evankravitz/ECE-3400-Team-1/resources/sensorposition.JPG

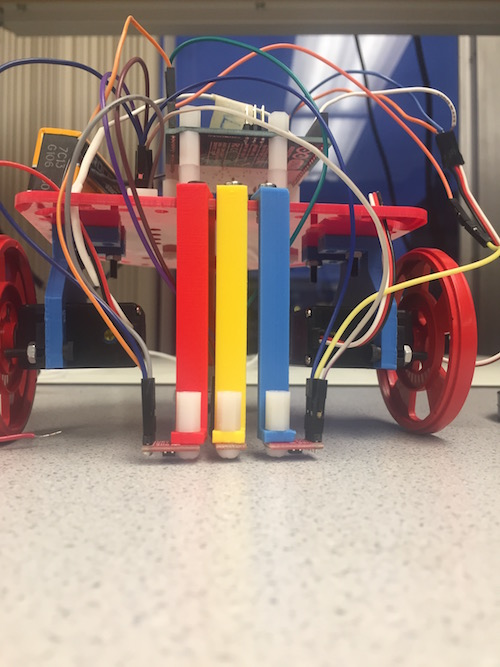
resources/sensorposition.JPG
