evankravitz/ECE-3400-Team-1/resources/lab2irscope.jpg

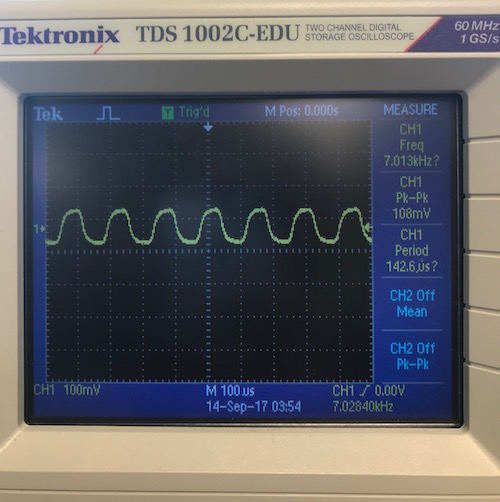
resources/lab2irscope.jpg
