evankravitz/ECE-3400-Team-1/img/portfolio/ethicsbot.gif

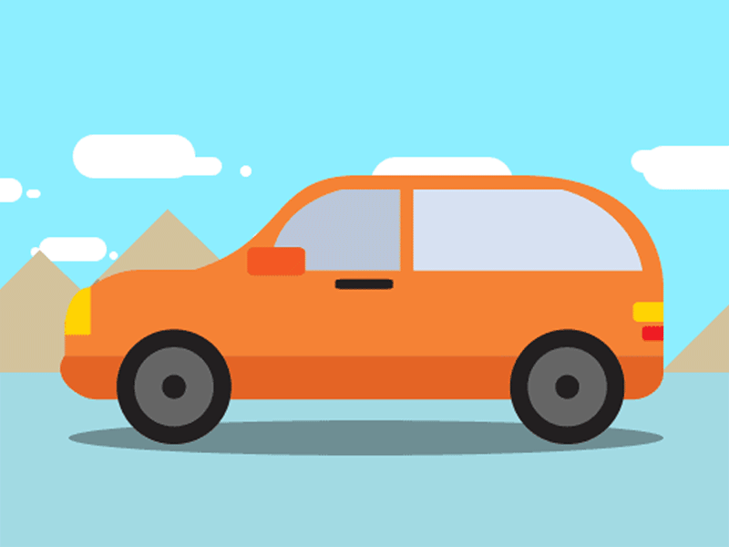
img/portfolio/ethicsbot.gif
