evankravitz/ECE-3400-Team-1/resources/2fc07050c8674d979eb9044ecb1724d5.jpeg

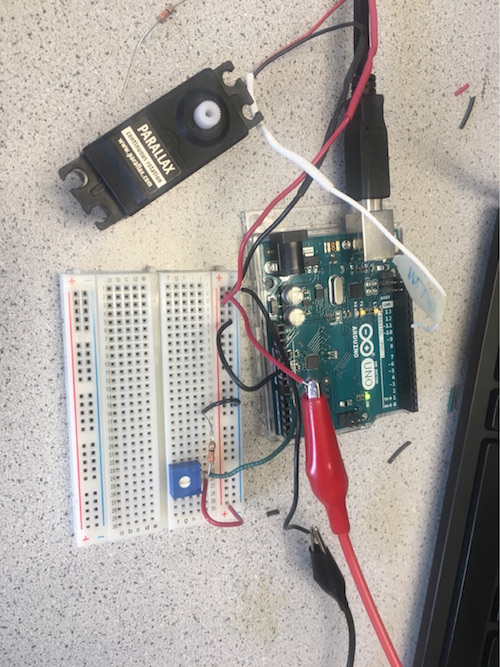
resources/2fc07050c8674d979eb9044ecb1724d5.jpeg
