evankravitz/ECE-3400-Team-1/resources/3f543bd7956b498f8c3eb461c208663a.jpeg

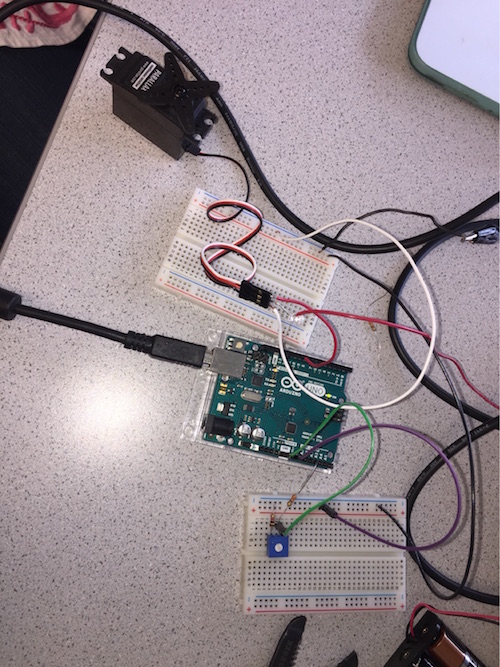
resources/3f543bd7956b498f8c3eb461c208663a.jpeg
