evankravitz/ECE-3400-Team-1/resources/6d352b7943044248b06bf93e79163291.jpeg

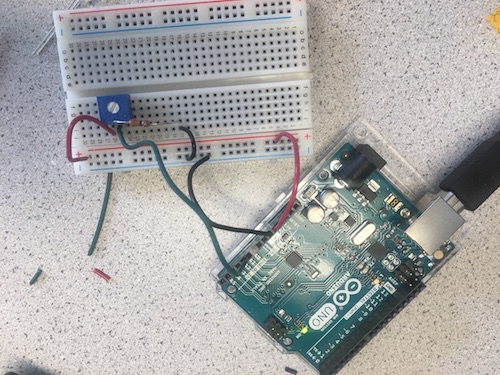
resources/6d352b7943044248b06bf93e79163291.jpeg
