evankravitz/ECE-3400-Team-1/resources/a3c3be304c904540ab26eccacc50d2ea.jpeg

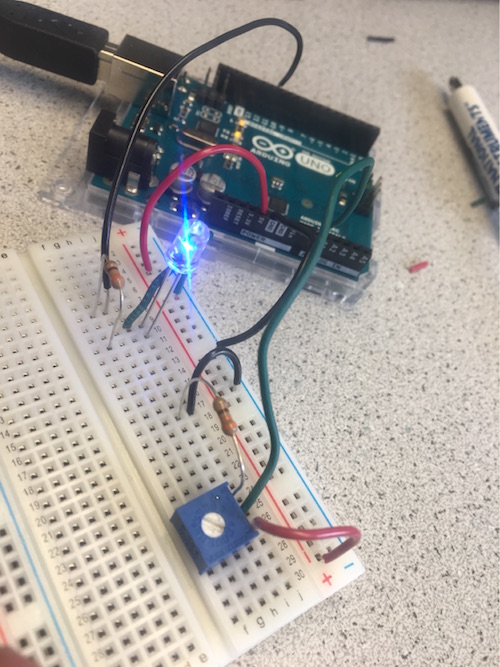
resources/a3c3be304c904540ab26eccacc50d2ea.jpeg
