evankravitz/ECE-3400-Team-1/resources/a6ba833ffcbe4ba188a3c3b04e216488.jpeg

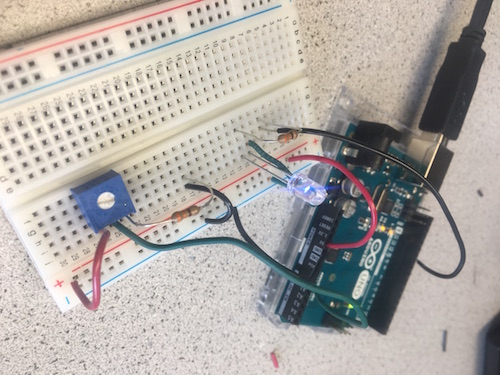
resources/a6ba833ffcbe4ba188a3c3b04e216488.jpeg
