evankravitz/ECE-3400-Team-1/resources/arduinocode_dfs.png

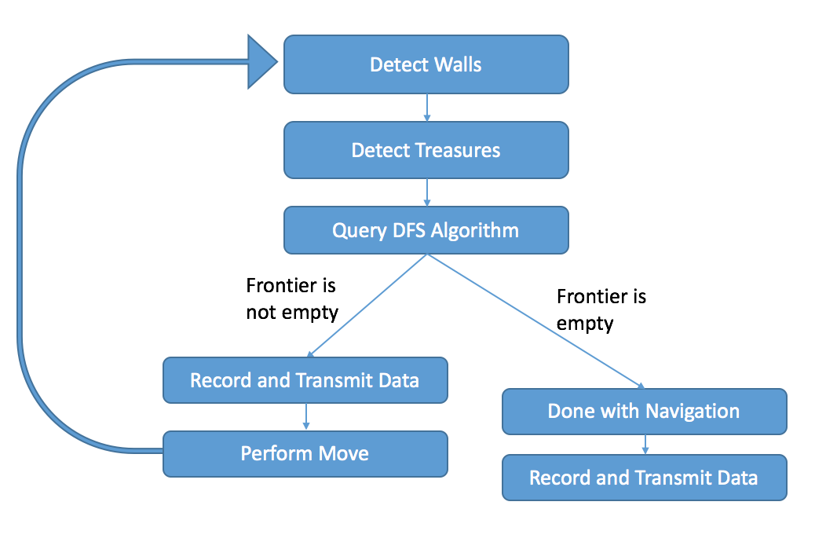
resources/arduinocode_dfs.png
