evankravitz/ECE-3400-Team-1/resources/back_bot.JPG

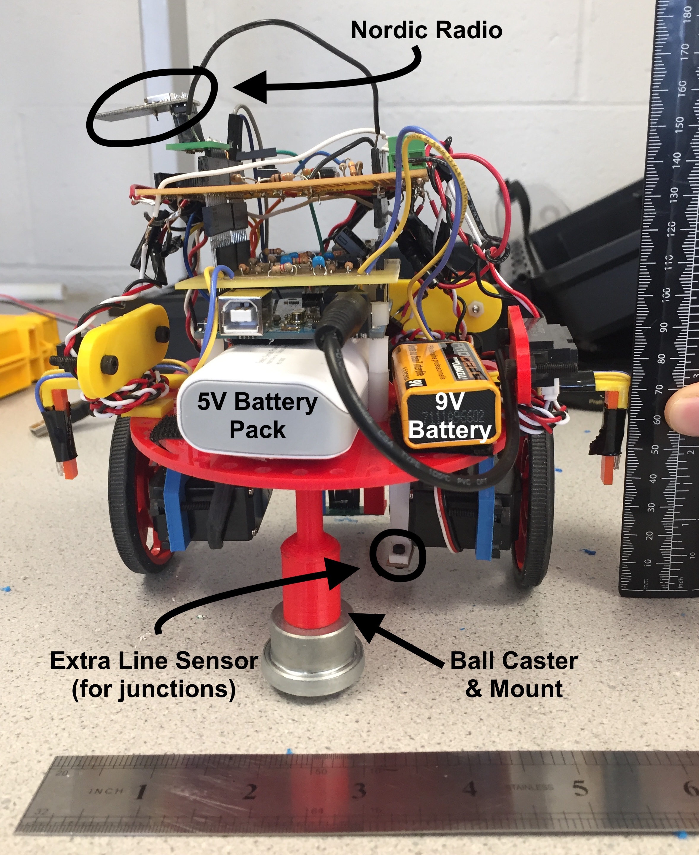
resources/back_bot.JPG
