evankravitz/ECE-3400-Team-1/resources/bigthirdplace.png

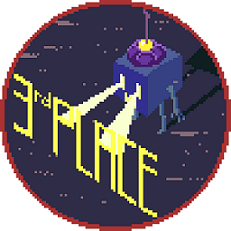
resources/bigthirdplace.png
