evankravitz/ECE-3400-Team-1/resources/bitdiagram.jpg

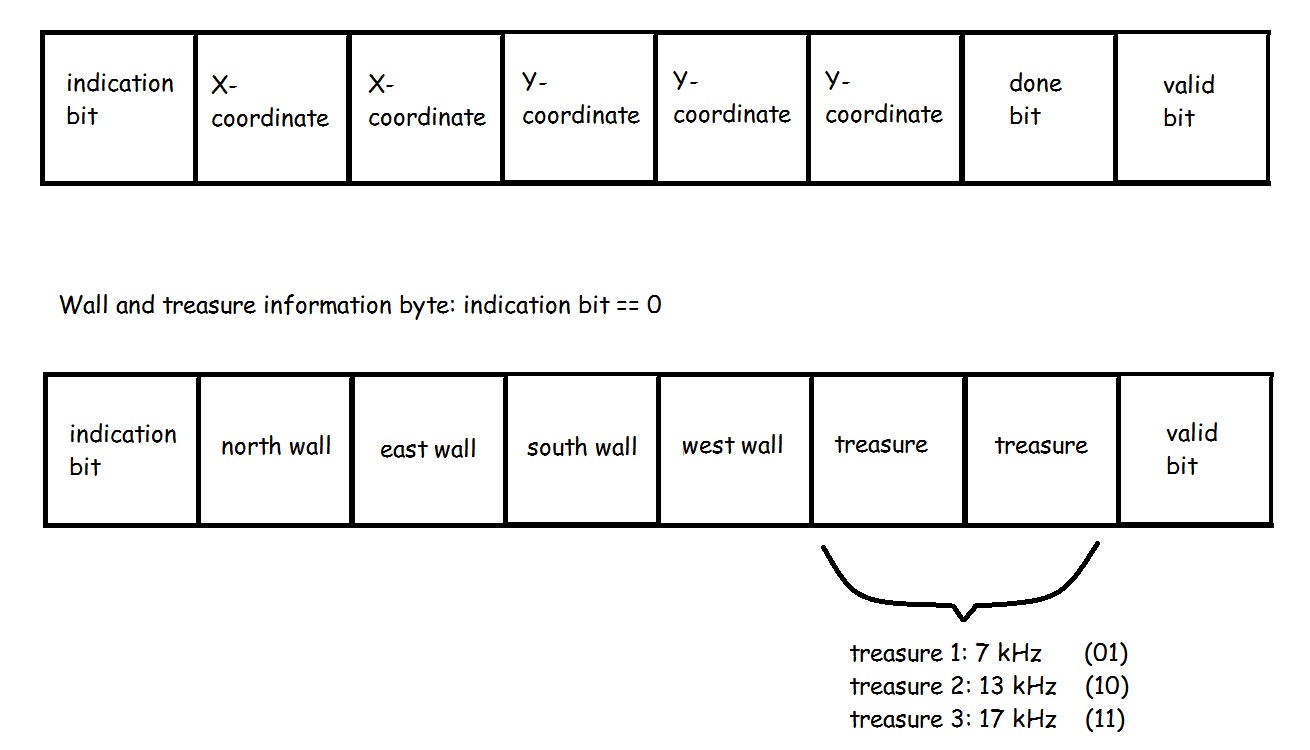
resources/bitdiagram.jpg
