evankravitz/ECE-3400-Team-1/resources/dfs_diagram.jpg

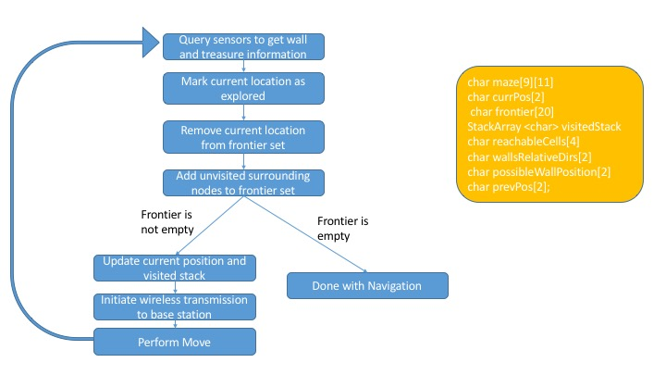
resources/dfs_diagram.jpg
