evankravitz/ECE-3400-Team-1/resources/FFT_660.png

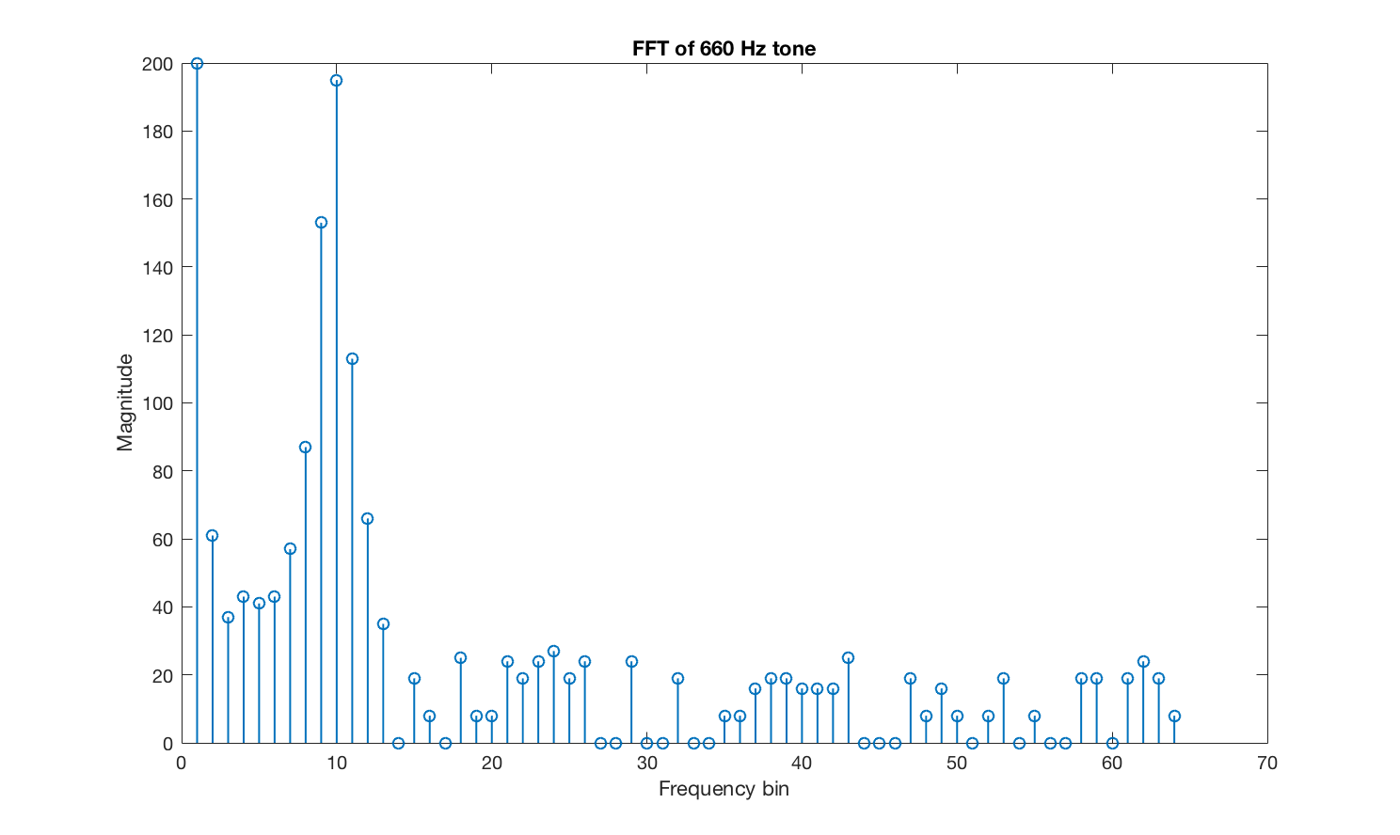
resources/FFT_660.png
