evankravitz/ECE-3400-Team-1/resources/fpgascreen.jpg

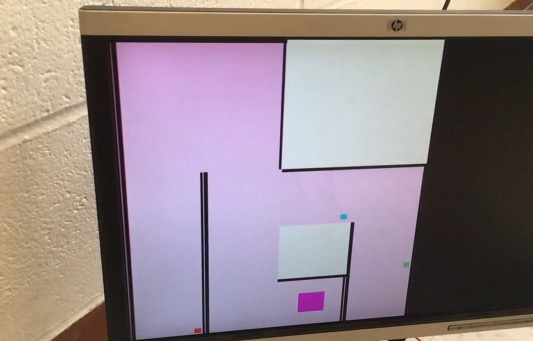
resources/fpgascreen.jpg
