evankravitz/ECE-3400-Team-1/resources/front_bot.JPG

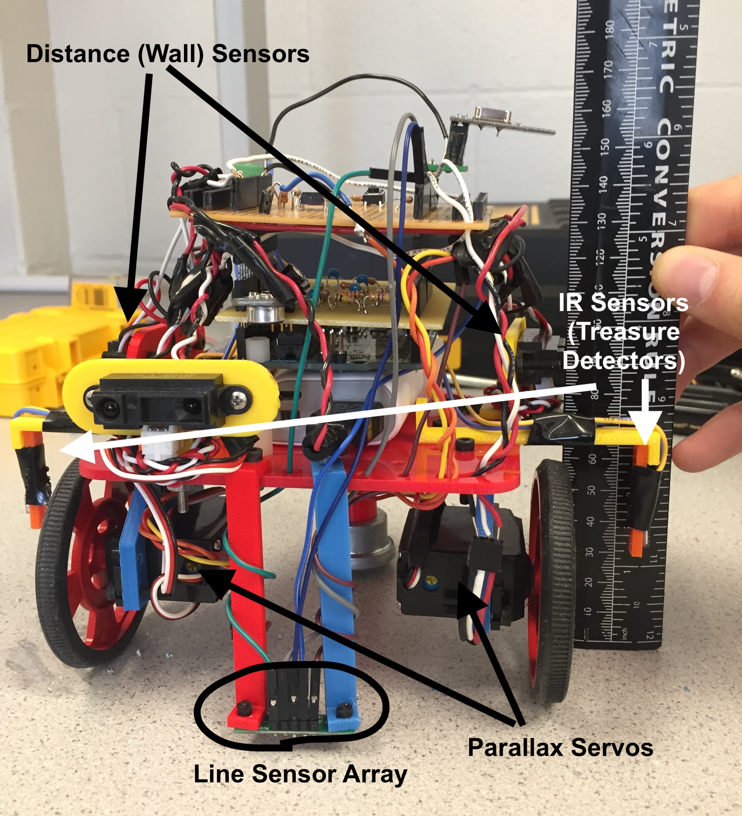
resources/front_bot.JPG
