evankravitz/ECE-3400-Team-1/resources/ircircuit.JPG

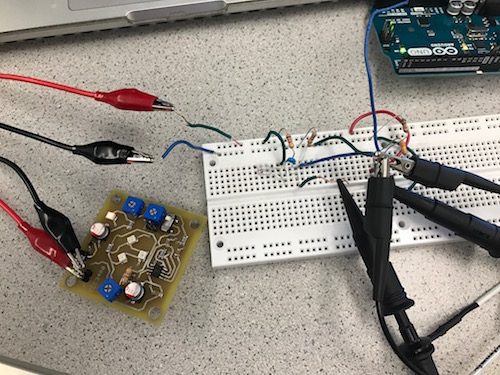
resources/ircircuit.JPG
