evankravitz/ECE-3400-Team-1/resources/irscope.JPG

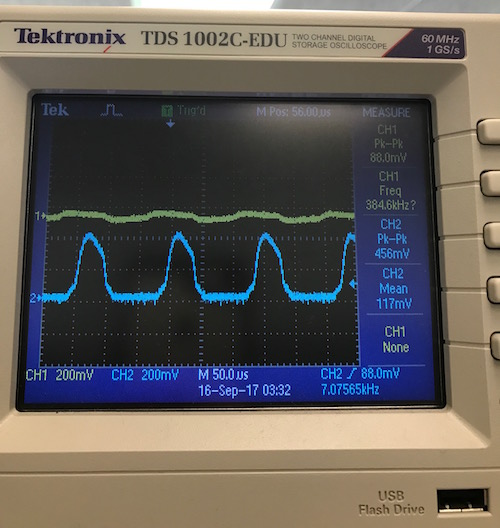
resources/irscope.JPG
