evankravitz/ECE-3400-Team-1/resources/lab1robot1.jpg

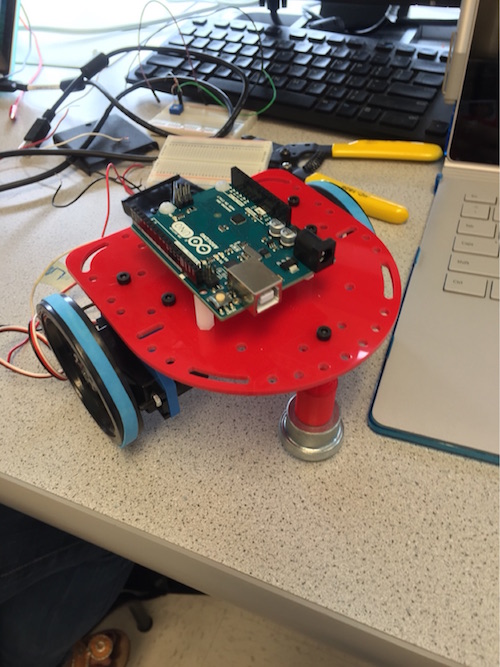
resources/lab1robot1.jpg
