evankravitz/ECE-3400-Team-1/resources/lab1robot2.jpg

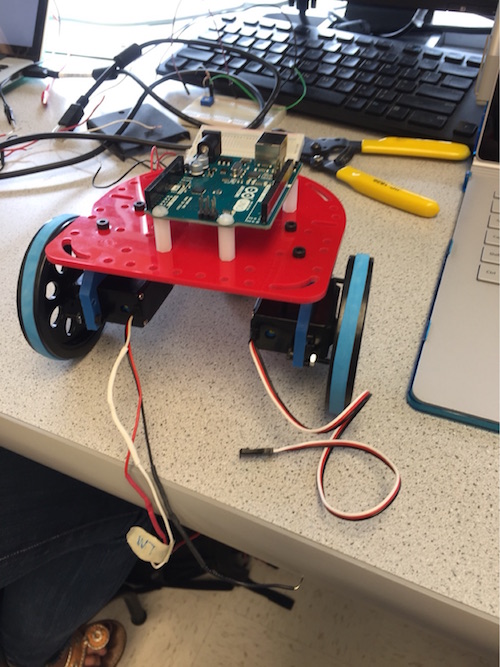
resources/lab1robot2.jpg
