evankravitz/ECE-3400-Team-1/resources/lab2_acoustic_data4.png

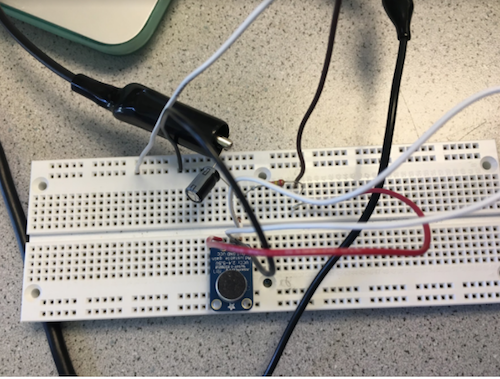
resources/lab2_acoustic_data4.png
