evankravitz/ECE-3400-Team-1/resources/lab2_acoustic_data5.png

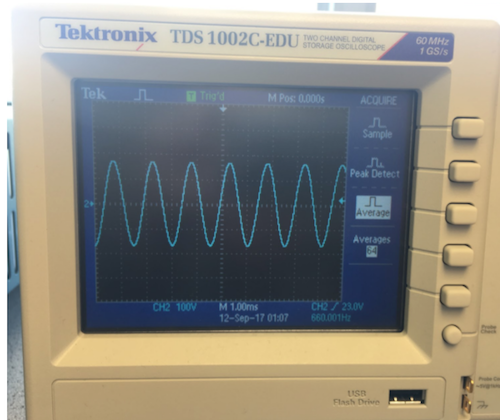
resources/lab2_acoustic_data5.png
