evankravitz/ECE-3400-Team-1/resources/lab2ircircuit.jpg

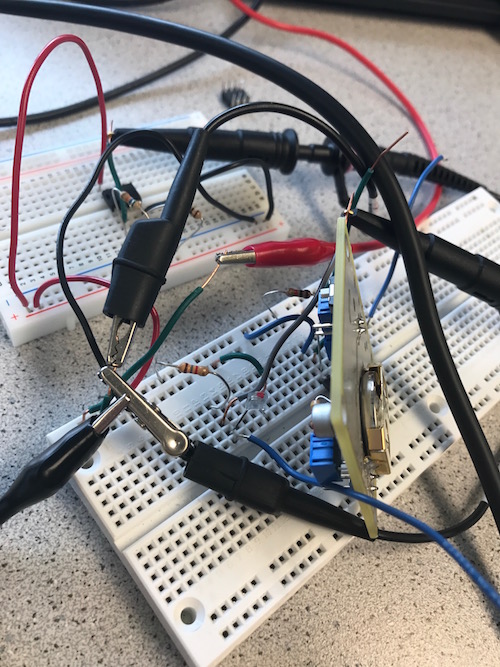
resources/lab2ircircuit.jpg
