evankravitz/ECE-3400-Team-1/resources/Microphone.png

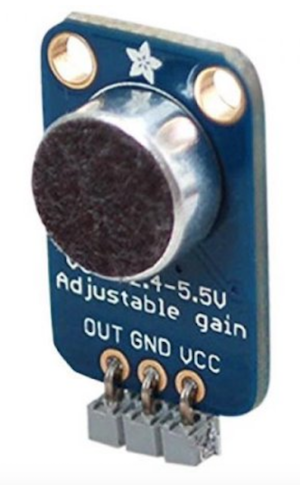
resources/Microphone.png
