evankravitz/ECE-3400-Team-1/resources/pcb.JPG

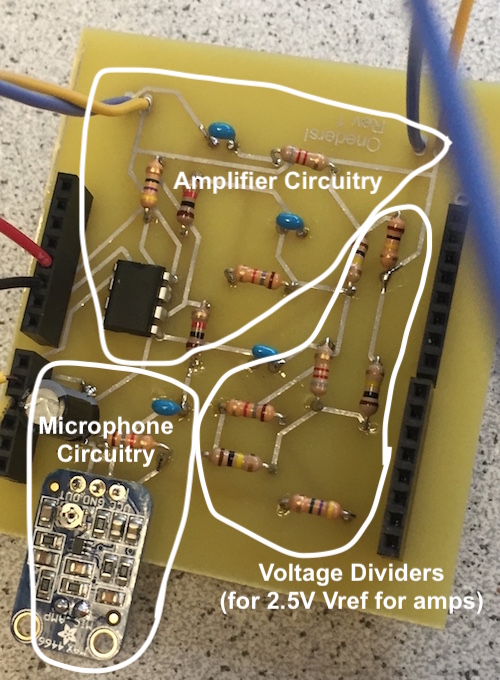
resources/pcb.JPG
