evankravitz/ECE-3400-Team-1/resources/protoboard.JPG

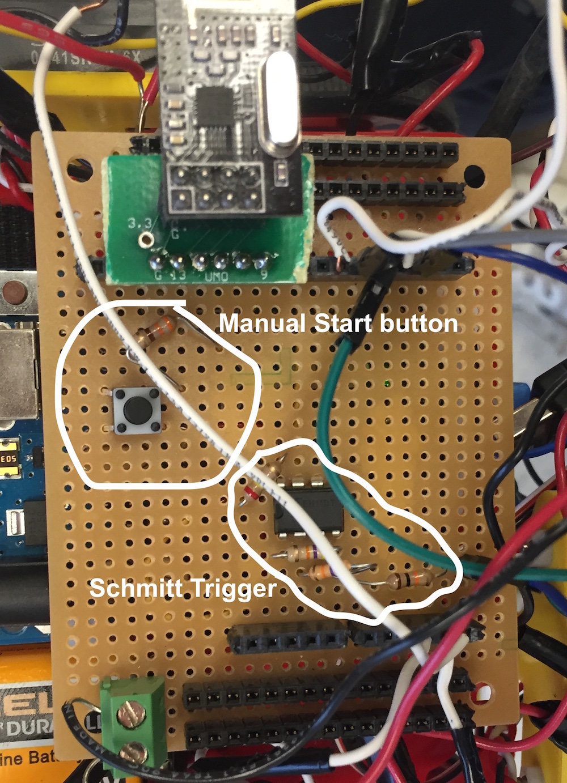
resources/protoboard.JPG
