evankravitz/ECE-3400-Team-1/resources/robotm3.jpg

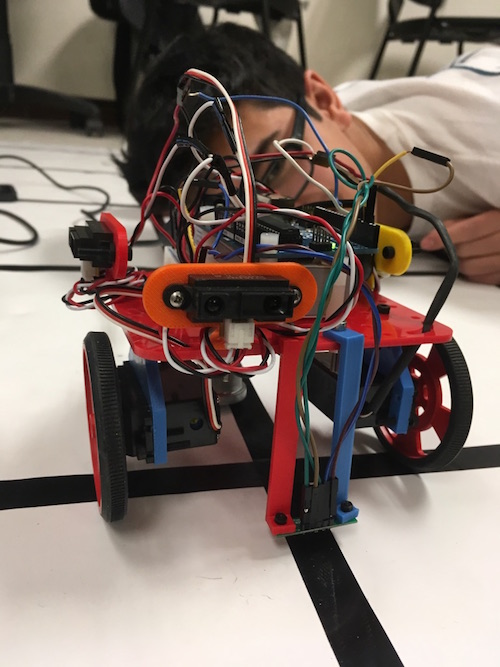
resources/robotm3.jpg
