evankravitz/ECE-3400-Team-1/resources/robotm4.JPG

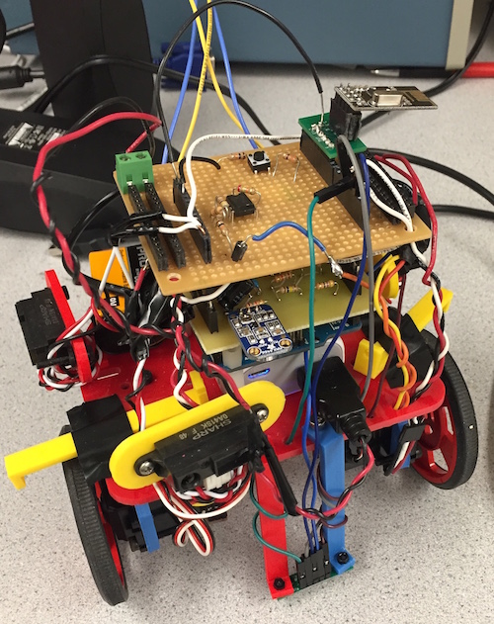
resources/robotm4.JPG
