evankravitz/ECE-3400-Team-1/resources/rotatedirscope.JPG

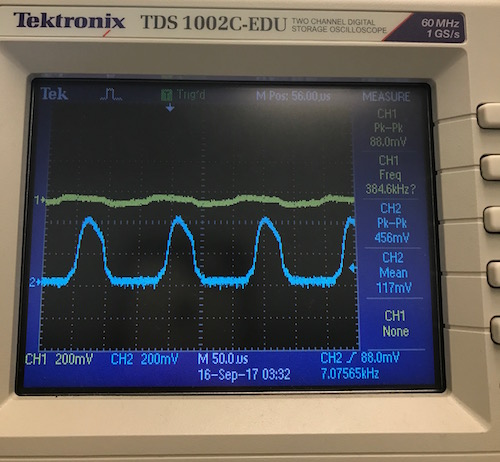
resources/rotatedirscope.JPG
