evankravitz/ECE-3400-Team-1/resources/schmitt_trigger.png

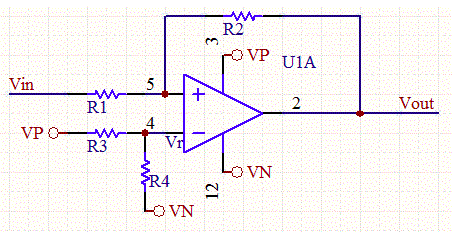
resources/schmitt_trigger.png
