evankravitz/ECE-3400-Team-1/resources/side_bot.JPG

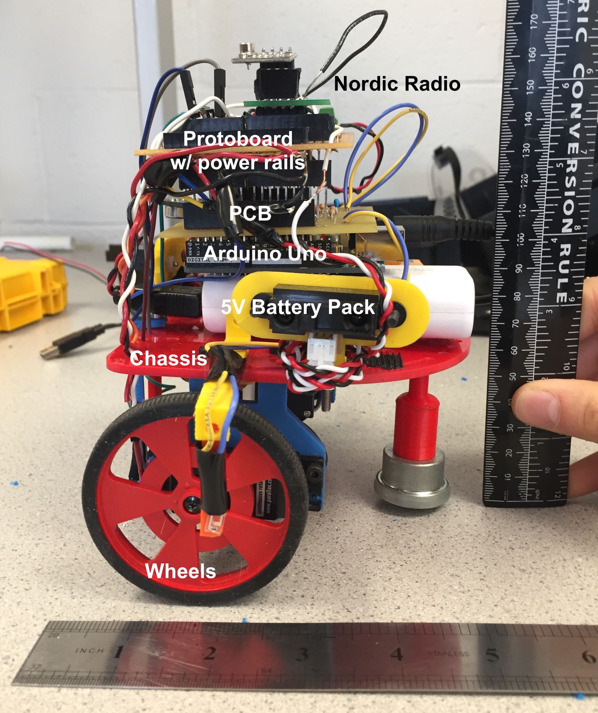
resources/side_bot.JPG
