evankravitz/ECE-3400-Team-1/resources/StartDetectLoop.png

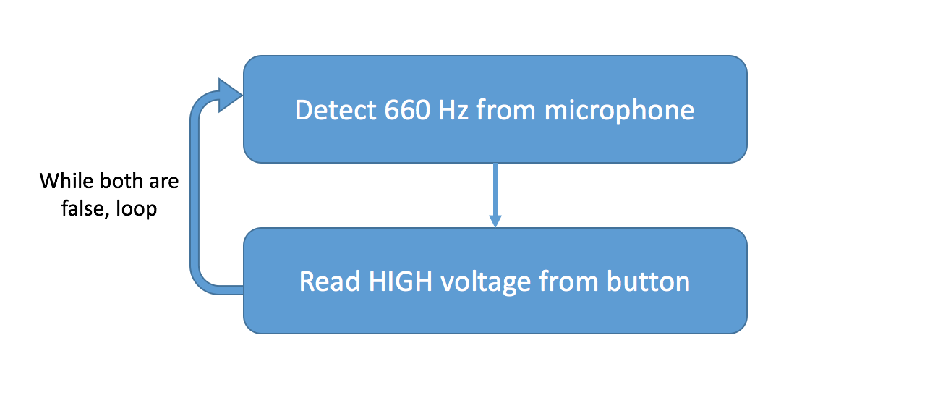
resources/StartDetectLoop.png
