evankravitz/ECE-3400-Team-1/resources/top_bot.JPG

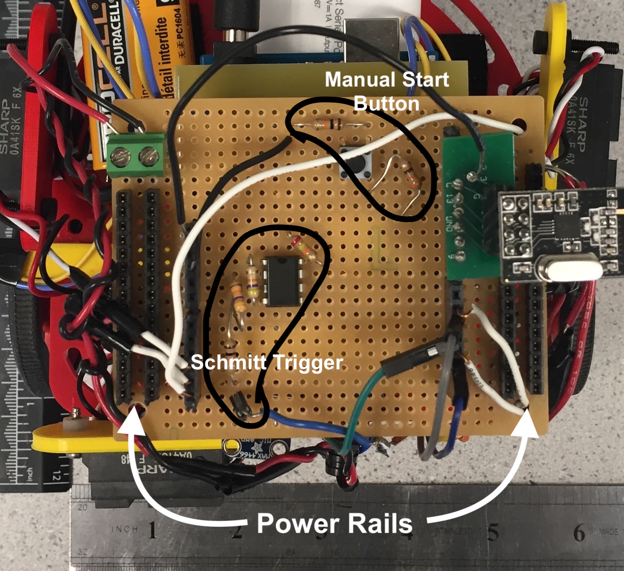
resources/top_bot.JPG
