evankravitz/ECE-3400-Team-1/resources/transmissionRobotDiagram.png

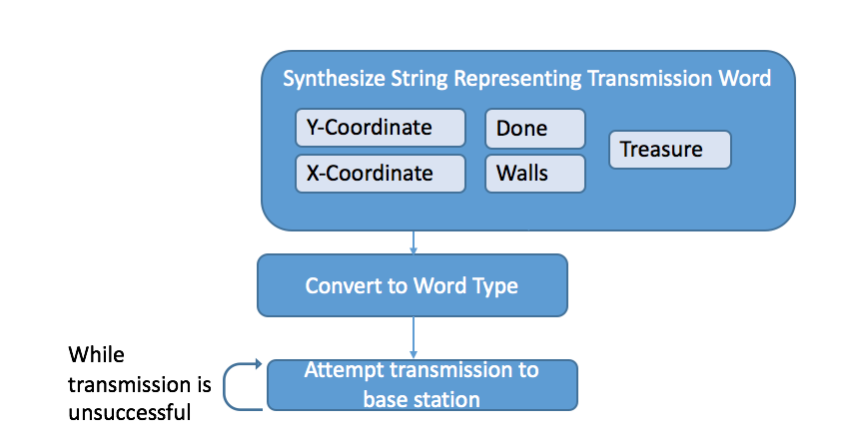
resources/transmissionRobotDiagram.png
