evankravitz/ECE-3400-Team-1/resources/Treasure-wave.JPG

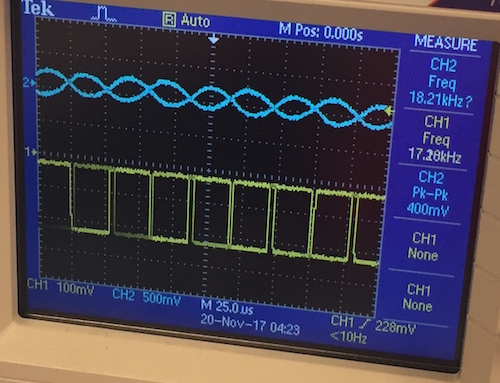
resources/Treasure-wave.JPG
