evankravitz/ECE-3400-Team-1/resources/treasuredetectiondiagram.png

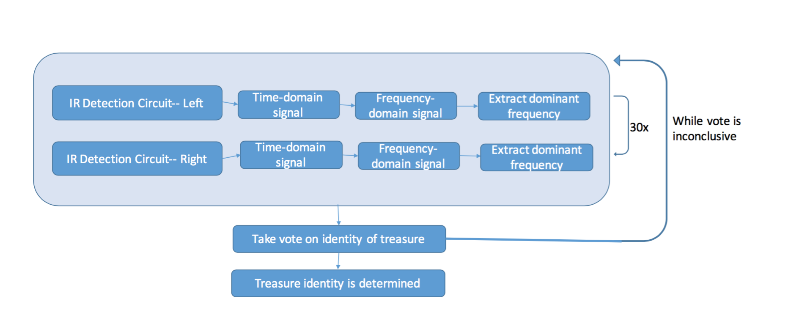
resources/treasuredetectiondiagram.png
