evankravitz/ECE-3400-Team-1/resources/trigger-wave.JPG

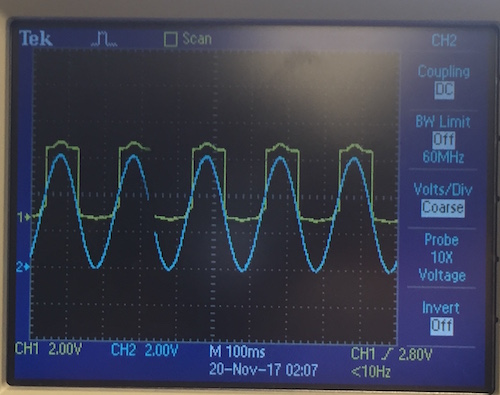
resources/trigger-wave.JPG
