evankravitz/ECE-3400-Team-1/resources/verilogdiagram.jpg

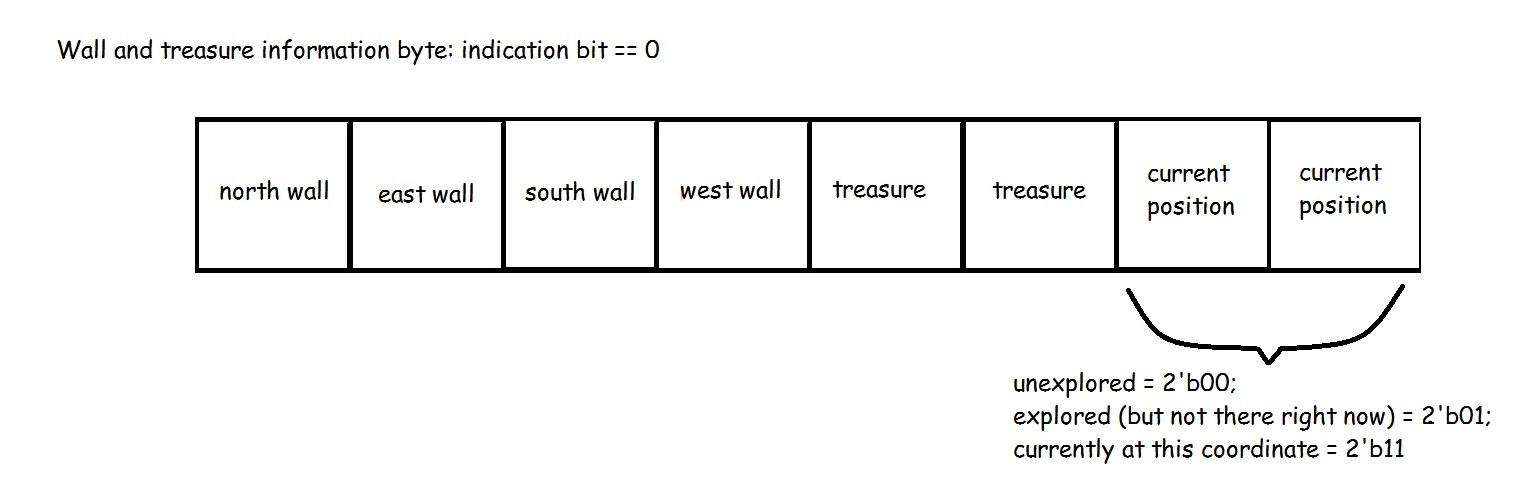
resources/verilogdiagram.jpg
