evankravitz/ECE-3400-Team-1/resources/whatever.jpg

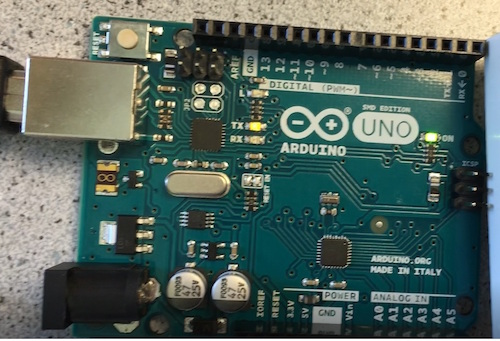
resources/whatever.jpg
