evankravitz/ECE-3400-Team-1/code dump/Final FPGA Code/GridSelector3.v

module GRID_SELECTOR(
CLOCK_50,
PIXEL_COORD_X,
PIXEL_COORD_Y,
GRID_X,
GRID_Y);


input CLOCK_50;
input wire [9:0] PIXEL_COORD_X;
input wire [9:0] PIXEL_COORD_Y;
output reg [3:0] GRID_X;
output reg [3:0] GRID_Y;




always @ (*) begin
	GRID_X = (PIXEL_COORD_X+1) / 96;
	GRID_Y = (PIXEL_COORD_Y) / 96;
end

	
endmodule
